ShehanHMK/Lead_acid_battery_charger/Simulation files ( LTSPICE )/Dual power supply.asc

C1: cap; 1000µ
C2: cap; 1000µ
C3: cap; 3000µ
D1: diode
D2: diode
D3: diode
D4: diode
D7: diode
D8: diode
L1: ind2; 10m
L2: ind2; {L}
L3: ind2; {L}
R1: res; 1
R2: res; 1k
R3: res; 1k
R4: res; 1k
V1: voltage; SINE(0 326 50)
Named nets: 0
k1 L1 L2 L3 1
.tran 2s uic
.param L=0.09m
