ShehanHMK/Lead_acid_battery_charger/Simulation files ( LTSPICE )/Final2cct.asc

12V_Relay: Relay
C1: cap; 187µF
C3: cap; 0.01µF
C4: cap; 1µ
Current_sense_resistor: res; 1
D1: schottky; MBR735
D3: zener; UDZV6_2B
D4: schottky; 30BQ060
D5: diode
L1: ind; 12.5mH
M1: nmos; IRF530
Q3: npn; 2N3019
Q5: npn; 2SD2700
R1: res; 10k
R2: res; 100k
R3: res; 1k
R4: res; 35k
R5: res; 30k
R6: res; 40k
R7: res; 330
R10: res; 5k
R11: res; 33k
R12: res; 10k
R13: res; 10k
R14: res; 51k
R15: res; 51k
R16: res; 10k
R17: res; 10k
R18: res; 33k
R19: res; 33k
R20: res; 1k
R21: res; 10k
R22: res; 10k
R23: res; 10k
R24: res; 10k
R25: res; 55k
R29: res; 10k
R30: res; 5k
R32: res; 1
R: res; 1k
U1: RH27C
U2: RH27C
U4: OP747
U5: OP747
U6: RH27C
U7: OP747
U9: OP747
V1: voltage; 30v
V2: voltage; 5.1
V3: voltage; 3.3v
V4: voltage; 15
V5: voltage; 15
V6: voltage; PWL(0 0 200m 3 400m 6 600m 9 800m 12 1000m 13 1.2 13.2 1.4 13.3 1.5 13.5 1.6 13.6 1.8 13.7 2 13.8)
Named nets: 0, Vcc, Vee, Vout1, Vout2, Compartor_Ref, PWM, Rsense+, Rsense-, Battery_ref, Vout3, Battery+
.tran 2s uic
POWER stage of the BUCK CONVERTER
1st Differential amplifier
Vout1 = 4.7( Delta V )
6.2V zener
Vout2 = 3.3 ( 5.1- Vin)  ; Vin = Vout1
Select the correct resistor depends on the zener diode
2nd Differential amplifier
Triangular Wave
Comparator
Astable Multivibrator
Square wave
Integrator
Constant Voltage Error amplifier
(3.3 - Battery_ref)
3rd Differential amplifier
Constant current controller
Relay driver
Load Simulation
LEAD ACID BATTERY CHARGER
13.75v
Comparator
Switching circuit  CC to CV at 13.8V
