ShehanHMK/Lead_acid_battery_charger/Simulation files ( LTSPICE )/Relay.asc

R1: res; 100
S1: sw; NO
S2: sw; NC
Named nets: +, -, COM, NO, NC
.model NO SW(Ron=1 Roff=10Meg Vt=11V )
.model NC SW(Ron=100Meg Roff=1 Vt=11V)
