ShehanHMK/Lead_acid_battery_charger/Simulation files ( LTSPICE )/Reverse polarity protection.asc

D1: diode; 1N4148
D2: schottky; 1N5818
M1: nmos; IRFZ44N
Q1: pnp; 2N2907
R1: res; 10k
R2: res; 10k
V1: voltage; PULSE(-12 12 0 1n 1n 1s 2s); Rser=1
V2: voltage; 14v
Named nets: 0
.tran 20s
